pimoroni/picade/picade-pcb/picade.sch

## EAGLE design picade-pcb/picade.sch (2015-05-28)

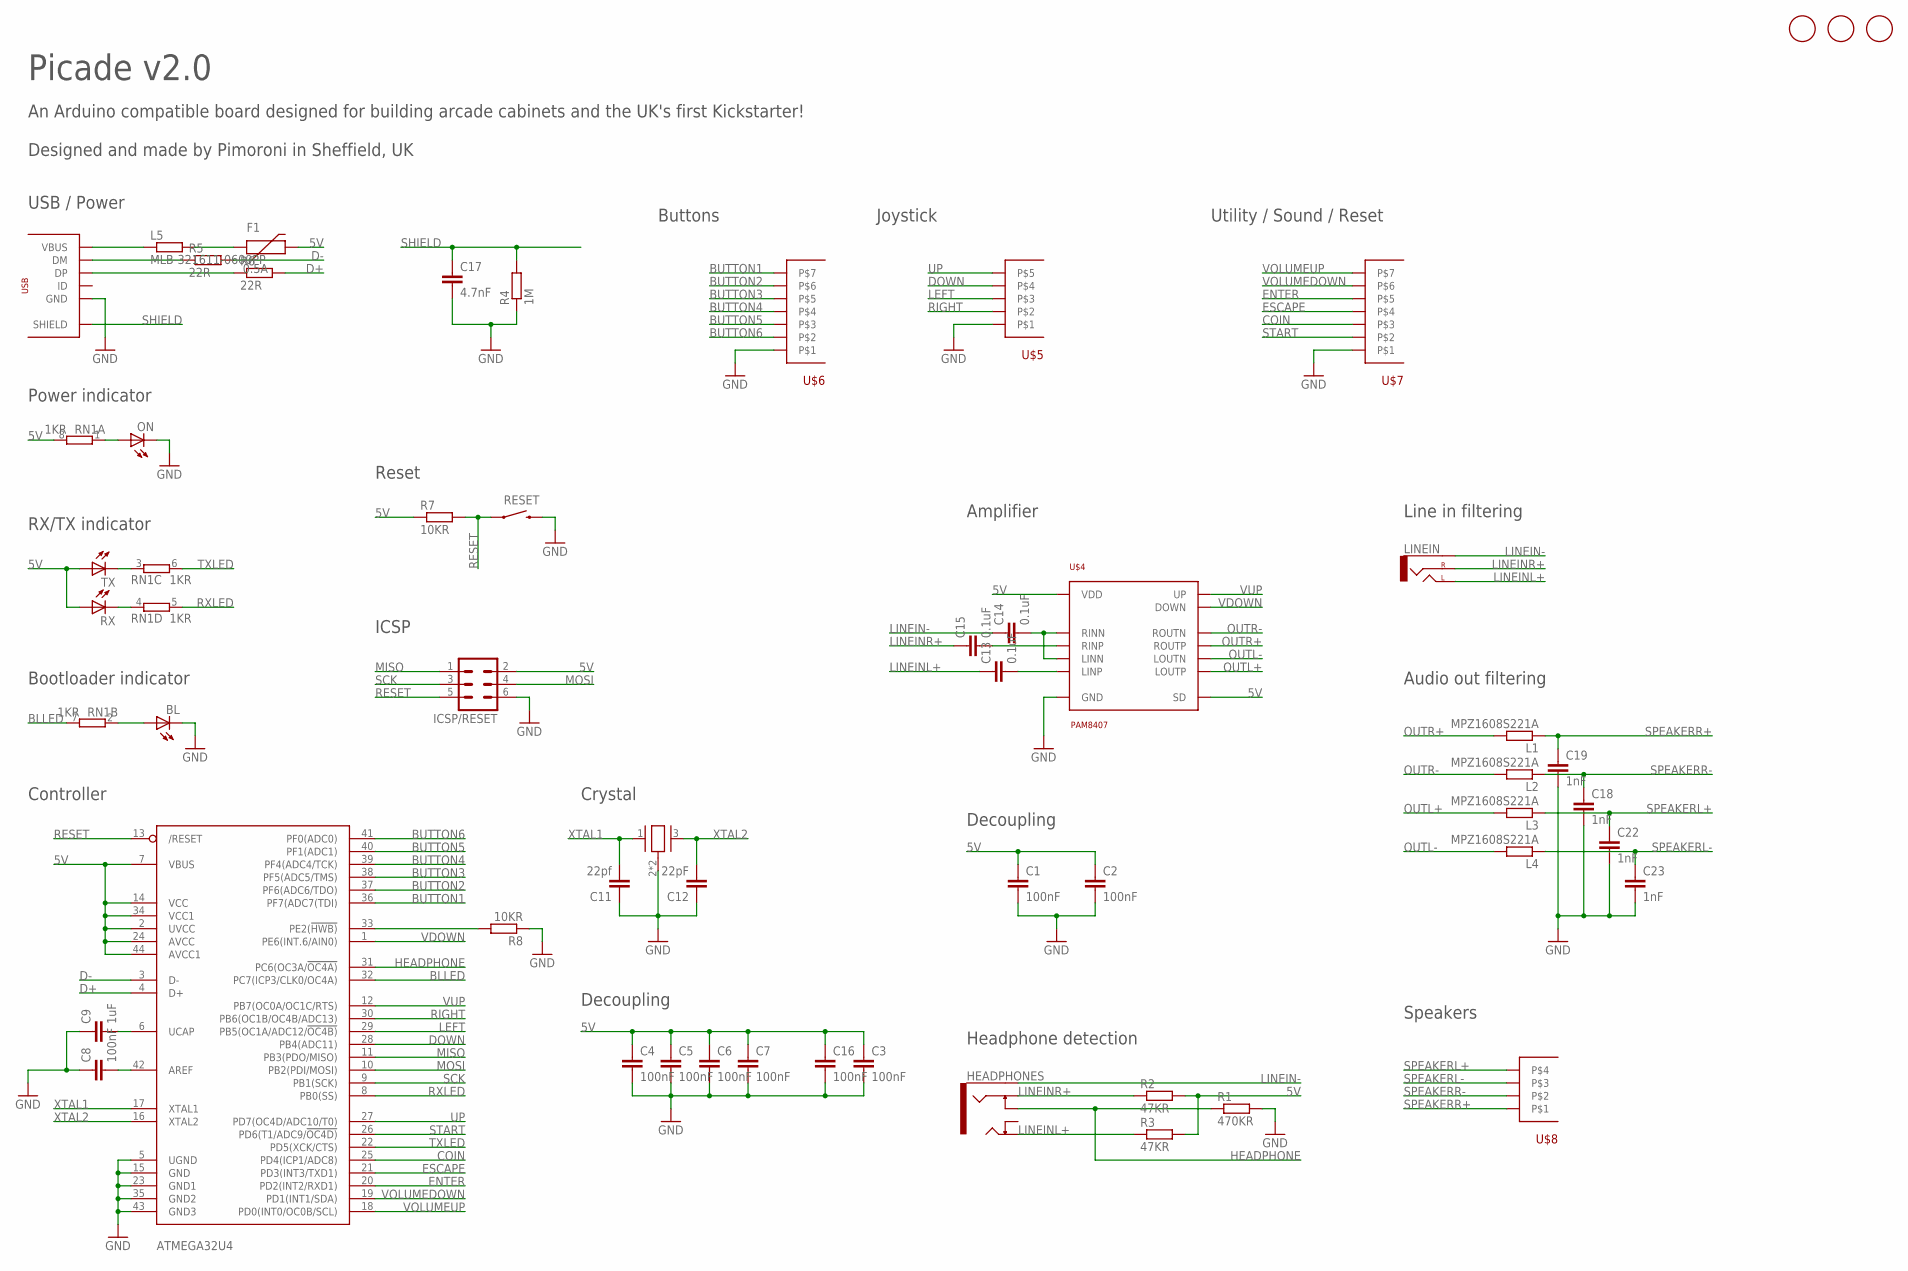
[picture p8: schematic picade.sch]

Parts:
16MHZ: TSX-3225
ATMEGA32U4: ATMEGA32U4-AU; TQFP44
BL: LEDCHIPLED_0805; CHIPLED_0805
C1, C2, C3, C4, C5, C6, C7, C8: 100nF; C0603K
C9: 1uF; C0603K
C11: 22pf; C0603K
C12: 22pF; C0603K
C13, C14, C15: 0.1uF; C0603K
C16: 100nF; C0805K
C17: 4.7nF; C0603K
C18, C19, C22, C23: 1nF; C0603K
F1: 0.5A; PTC-1206
HEADPHONES: stereo-jack-switched; AUDIO-JACK-3.5MM-SMD
ICSP/RESET: MA03-2
L1, L2, L3, L4: MPZ1608S221A; R0603
L5: MLB-321611-0600PP; R1206
LINEIN: stereo-jack-noswitch; AUDIO-JACK-3.5MM-SMD
ON: LEDCHIPLED_0805; CHIPLED_0805
R1: 470KR; R0603
R2, R3: 47KR; R0603
R4: 1M; R0603
R5, R6: 22R; R0603
R7, R8: 10KR; R0603
RESET: gullwing-switch; TACTILE-SWITCH-1101NE
RN1: 1KR; 0603-ARC
RX: LEDCHIPLED_0805; CHIPLED_0805
TX: LEDCHIPLED_0805; CHIPLED_0805
U$1, U$2, U$3: FIDUCIAL1MM; FIDUCIAL-1MM
U$4: PAM8407; SO-16
U$5: 5-WAY; 1X5-3.5MM-SCREWTERMINAL
U$6, U$7: 7-WAY; 1X7-3.5MM-SCREWTERMINAL
U$8: 4-WAY; 1X4-3.5MM-SCREWTERMINAL
U$13: USBMICROB; MICROB-USB

Connections:
5V: ATMEGA32U4.2 (UVCC), ATMEGA32U4.7 (VBUS), ATMEGA32U4.14 (VCC), ATMEGA32U4.24 (AVCC), ATMEGA32U4.34 (VCC1), ATMEGA32U4.44 (AVCC1), C1.1, C2.1, C3.1, C4.1, C5.1, C6.1, C7.1, C16.1, F1.2, ICSP/RESET.2, R2.2, R3.2, R7.1, RN1.8 (2), RX.A, TX.A, U$4.3 (SD), U$4.9 (VDD)
BLLED: ATMEGA32U4.32 (PC7(ICP3/CLK0/OC4A)), RN1.7 (2)
BUTTON1: ATMEGA32U4.36 (PF7(ADC7(TDI)), U$6.7
BUTTON2: ATMEGA32U4.37 (PF6(ADC6/TDO)), U$6.6
BUTTON3: ATMEGA32U4.38 (PF5(ADC5/TMS)), U$6.5
BUTTON4: ATMEGA32U4.39 (PF4(ADC4/TCK)), U$6.4
BUTTON5: ATMEGA32U4.40 (PF1(ADC1)), U$6.3
BUTTON6: ATMEGA32U4.41 (PF0(ADC0)), U$6.2
COIN: ATMEGA32U4.25 (PD4(ICP1/ADC8)), U$7.3
D+: ATMEGA32U4.4 (D+), R6.2
D-: ATMEGA32U4.3 (D-), R5.2
DOWN: ATMEGA32U4.28 (PB4(ADC11)), U$5.4
ENTER: ATMEGA32U4.20 (PD2(INT2/RXD1)), U$7.5
ESCAPE: ATMEGA32U4.21 (PD3(INT3/TXD1)), U$7.4
GND: 16MHZ.2 (GND), ATMEGA32U4.5 (UGND), ATMEGA32U4.15 (GND), ATMEGA32U4.23 (GND1), ATMEGA32U4.35 (GND2), ATMEGA32U4.43 (GND3), BL.C, C1.2, C2.2, C3.2, C4.2, C5.2, C6.2, C7.2, C8.1, C9.1, C11.1, C12.1, C16.2, C17.2, C18.2, C19.2, C22.2, C23.2, ICSP/RESET.6, ON.C, R1.2, R4.1, R8.1, RESET.P$2 (2), U$4.6 (GND), U$5.1, U$6.1, U$7.1, U$13.GND
HEADPHONE: ATMEGA32U4.31 (PC6(OC3A/!OC4A)), HEADPHONES.RSH, R1.1
LEFT: ATMEGA32U4.29 (PB5(OC1A/ADC12/!OC4B)), U$5.3
LIENINLCAP: C13.2, U$4.8 (LINP)
LINEIN-: C14.1, HEADPHONES.SLEEVE, LINEIN.SLEEVE
LINEINL+: C13.1, HEADPHONES.TIP, LINEIN.TIP (LEFT), R3.1
LINEINR+: C15.1, HEADPHONES.RING, LINEIN.RING (RIGHT), R2.1
LINEINRCAP: C15.2, U$4.1 (RINP)
MISO: ATMEGA32U4.11 (PB3(PDO/MISO)), ICSP/RESET.1
MOSI: ATMEGA32U4.10 (PB2(PDI/MOSI)), ICSP/RESET.4
unnamed: ATMEGA32U4.6 (UCAP), C9.2
unnamed: ON.A, RN1.1
unnamed: R5.1, U$13.DM
unnamed: R6.1, U$13.DP
unnamed: ATMEGA32U4.42 (AREF), C8.2
unnamed: BL.A, RN1.2 (1)
unnamed: F1.1, L5.2
unnamed: C14.2, U$4.2 (RINN), U$4.7 (LINN)
unnamed: RN1.3 (1), TX.C
unnamed: RN1.4 (1), RX.C
unnamed: ATMEGA32U4.33 (PE2(!HWB)), R8.2
OUTL+: L3.2, U$4.10 (LOUTP)
OUTL-: L4.2, U$4.11 (LOUTN)
OUTR+: L1.2, U$4.15 (ROUTP)
OUTR-: L2.2, U$4.14 (ROUTN)
RESET: ATMEGA32U4.13 (/RESET), ICSP/RESET.5, R7.2, RESET.P$1 (1)
RIGHT: ATMEGA32U4.30 (PB6(OC1B/OC4B/ADC13)), U$5.2
RXLED: ATMEGA32U4.8 (PB0(SS)), RN1.5 (2)
SCK: ATMEGA32U4.9 (PB1(SCK)), ICSP/RESET.3
SHIELD: C17.1, R4.2, U$13.SH1 (SHIELD)
SPEAKERL+: C22.1, L3.1, U$8.4
SPEAKERL-: C23.1, L4.1, U$8.3
SPEAKERR+: C19.1, L1.1, U$8.1
SPEAKERR-: C18.1, L2.1, U$8.2
START: ATMEGA32U4.26 (PD6(T1/ADC9/!OC4D)), U$7.2
TXLED: ATMEGA32U4.22 (PD5(XCK/CTS)), RN1.6 (2)
UP: ATMEGA32U4.27 (PD7(OC4D/ADC10/T0)), U$5.5
VBUS: L5.1, U$13.VBUS
VDOWN: ATMEGA32U4.1 (PE6(INT.6/AIN0)), U$4.5 (DOWN)
VOLUMEDOWN: ATMEGA32U4.19 (PD1(INT1/SDA)), U$7.6
VOLUMEUP: ATMEGA32U4.18 (PD0(INT0/OC0B/SCL)), U$7.7
VUP: ATMEGA32U4.12 (PB7(OC0A/OC1C/RTS)), U$4.4 (UP)
XTAL1: 16MHZ.1 (XIN), ATMEGA32U4.17 (XTAL1), C11.2
XTAL2: 16MHZ.3 (XOUT), ATMEGA32U4.16 (XTAL2), C12.2

Notes on the sheet:
Line in filtering
Utility / Sound / Reset
Picade v2.0
An Arduino compatible board designed for building arcade cabinets and the UK's first Kickstarter! Designed and made by Pimoroni in Sheffield, UK
Buttons
Joystick
Amplifier
Controller
Speakers
USB / Power
Power indicator
Decoupling
Reset
ICSP
Crystal
RX/TX indicator
Bootloader indicator
Headphone detection
Audio out filtering
